Ranthalion/ButtonRelayControl/firmware/ButtonRelayControl/ButtonRelayControl/src/driver_init.c

/**
 * \file
 *
 * \brief Driver initialization.
 *
 (c) 2018 Microchip Technology Inc. and its subsidiaries.

    Subject to your compliance with these terms,you may use this software and
    any derivatives exclusively with Microchip products.It is your responsibility
    to comply with third party license terms applicable to your use of third party
    software (including open source software) that may accompany Microchip software.

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
    IN NO EVENT WILL MICROCHIP BE LIABLE FOR ANY INDIRECT, SPECIAL, PUNITIVE,
    INCIDENTAL OR CONSEQUENTIAL LOSS, DAMAGE, COST OR EXPENSE OF ANY KIND
    WHATSOEVER RELATED TO THE SOFTWARE, HOWEVER CAUSED, EVEN IF MICROCHIP HAS
    BEEN ADVISED OF THE POSSIBILITY OR THE DAMAGES ARE FORESEEABLE. TO THE
    FULLEST EXTENT ALLOWED BY LAW, MICROCHIP'S TOTAL LIABILITY ON ALL CLAIMS IN
    ANY WAY RELATED TO THIS SOFTWARE WILL NOT EXCEED THE AMOUNT OF FEES, IF ANY,
    THAT YOU HAVE PAID DIRECTLY TO MICROCHIP FOR THIS SOFTWARE.
 *
 */

/*
 * Code generated by START.
 *
 * This file will be overwritten when reconfiguring your START project.
 * Please copy examples or other code you want to keep to a separate file
 * to avoid losing it when reconfiguring.
 */

#include "driver_init.h"
#include <system.h>

void EXTERNAL_IRQ_0_initialization(void)
{

	// Set pin direction to input
	SW1_set_dir(PORT_DIR_IN);

	SW1_set_pull_mode(
	    // <y> Pull configuration
	    // <id> pad_pull_config
	    // <PORT_PULL_OFF"> Off
	    // <PORT_PULL_UP"> Pull-up
	    PORT_PULL_UP);

	// Set pin direction to input
	SENS2_set_dir(PORT_DIR_IN);

	SENS2_set_pull_mode(
	    // <y> Pull configuration
	    // <id> pad_pull_config
	    // <PORT_PULL_OFF"> Off
	    // <PORT_PULL_UP"> Pull-up
	    PORT_PULL_OFF);

	// Set pin direction to input
	SENS1_set_dir(PORT_DIR_IN);

	SENS1_set_pull_mode(
	    // <y> Pull configuration
	    // <id> pad_pull_config
	    // <PORT_PULL_OFF"> Off
	    // <PORT_PULL_UP"> Pull-up
	    PORT_PULL_OFF);

	// Set pin direction to input
	SW2_set_dir(PORT_DIR_IN);

	SW2_set_pull_mode(
	    // <y> Pull configuration
	    // <id> pad_pull_config
	    // <PORT_PULL_OFF"> Off
	    // <PORT_PULL_UP"> Pull-up
	    PORT_PULL_UP);

	EXTERNAL_IRQ_0_init();
}

void LED_SW2_initialization(void)
{

	// Set pin direction to output
	PD6_set_dir(PORT_DIR_OUT);

	PD6_set_level(
	    // <y> Initial level
	    // <id> pad_initial_level
	    // <false"> Low
	    // <true"> High
	    true);

	LED_SW2_init();
}

void LED_SW1_initialization(void)
{

	// Set pin direction to output
	PB1_set_dir(PORT_DIR_OUT);

	PB1_set_level(
	    // <y> Initial level
	    // <id> pad_initial_level
	    // <false"> Low
	    // <true"> High
	    true);

	LED_SW1_init();
}

void TIMER_0_initialization(void)
{

	TIMER_0_timeout_init();
}

/**
 * \brief System initialization
 */
void system_init()
{
	mcu_init();

	/* PORT setting on PB6 */

	// Set pin direction to output
	RELAY1_set_dir(PORT_DIR_OUT);

	RELAY1_set_level(
	    // <y> Initial level
	    // <id> pad_initial_level
	    // <false"> Low
	    // <true"> High
	    false);

	/* PORT setting on PD0 */

	// Set pin direction to output
	LED_set_dir(PORT_DIR_OUT);

	LED_set_level(
	    // <y> Initial level
	    // <id> pad_initial_level
	    // <false"> Low
	    // <true"> High
	    true);

	/* PORT setting on PE1 */

	// Set pin direction to output
	RELAY2_set_dir(PORT_DIR_OUT);

	RELAY2_set_level(
	    // <y> Initial level
	    // <id> pad_initial_level
	    // <false"> Low
	    // <true"> High
	    false);

	sysctrl_init();

	EXTERNAL_IRQ_0_initialization();

	LED_SW2_initialization();

	LED_SW1_initialization();

	TIMER_0_initialization();
}
