Ranthalion/ButtonRelayControl/firmware/ButtonRelayControl/ButtonRelayControl/src/timeout.c

/**
 * \file
 *
 * \brief Timeout driver.
 *
 (c) 2018 Microchip Technology Inc. and its subsidiaries.

    Subject to your compliance with these terms,you may use this software and
    any derivatives exclusively with Microchip products.It is your responsibility
    to comply with third party license terms applicable to your use of third party
    software (including open source software) that may accompany Microchip software.

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
    IN NO EVENT WILL MICROCHIP BE LIABLE FOR ANY INDIRECT, SPECIAL, PUNITIVE,
    INCIDENTAL OR CONSEQUENTIAL LOSS, DAMAGE, COST OR EXPENSE OF ANY KIND
    WHATSOEVER RELATED TO THE SOFTWARE, HOWEVER CAUSED, EVEN IF MICROCHIP HAS
    BEEN ADVISED OF THE POSSIBILITY OR THE DAMAGES ARE FORESEEABLE. TO THE
    FULLEST EXTENT ALLOWED BY LAW, MICROCHIP'S TOTAL LIABILITY ON ALL CLAIMS IN
    ANY WAY RELATED TO THIS SOFTWARE WILL NOT EXCEED THE AMOUNT OF FEES, IF ANY,
    THAT YOU HAVE PAID DIRECTLY TO MICROCHIP FOR THIS SOFTWARE.
 *
 */

/**
 \defgroup doc_driver_timer_timeout Timeout Driver
 \ingroup doc_driver_timer

 \section doc_driver_timer_timeout_rev Revision History
 - v0.0.0.1 Initial Commit

@{
*/
#include <stdio.h>
#include "timeout.h"
#include "atomic.h"

absolutetime_t TIMER_0_dummy_handler(void *payload)
{
	return 0;
};

void           TIMER_0_start_timer_at_head(void);
void           TIMER_0_enqueue_callback(timer_struct_t *timer);
void           TIMER_0_set_timer_duration(absolutetime_t duration);
absolutetime_t TIMER_0_make_absolute(absolutetime_t timeout);
absolutetime_t TIMER_0_rebase_list(void);

timer_struct_t *TIMER_0_list_head          = NULL;
timer_struct_t *TIMER_0_execute_queue_head = NULL;

timer_struct_t          TIMER_0_dummy                         = {TIMER_0_dummy_handler};
volatile absolutetime_t TIMER_0_absolute_time_of_last_timeout = 0;
volatile absolutetime_t TIMER_0_last_timer_load               = 0;
volatile bool           TIMER_0_is_running                    = false;

void TIMER_0_timeout_init(void)
{

	/* Enable TC3 */
	PRR1 &= ~(1 << PRTIM3);

	// TCCR3A = (0 << COM3A1) | (0 << COM3A0) /* Normal port operation, OCA disconnected */
	//		 | (0 << COM3B1) | (0 << COM3B0) /* Normal port operation, OCB disconnected */
	//		 | (0 << WGM31) | (0 << WGM30); /* Timeout */

	TCCR3B = (0 << WGM33) | (0 << WGM32)                /* Timeout */
	         | 0 << ICNC3                               /* Input Capture Noise Canceler: disabled */
	         | 0 << ICES3                               /* Input Capture Edge Select: disabled */
	         | (1 << CS32) | (0 << CS31) | (1 << CS30); /* IO clock divided by 1024 */

	TIMSK3 = 0 << OCIE3B   /* Output Compare B Match Interrupt Enable: disabled */
	         | 0 << OCIE3A /* Output Compare A Match Interrupt Enable: disabled */
	         | 0 << ICIE3  /* Input Capture Interrupt Enable: disabled */
	         | 1 << TOIE3; /* Overflow Interrupt Enable: enabled */
}

// Disable all the timers without deleting them from any list. Timers can be
//    restarted by calling startTimerAtHead
void TIMER_0_stop_timeouts(void)
{
	TIMSK3 &= ~(1 << TOIE3);

	TIMER_0_absolute_time_of_last_timeout = 0;
	TIMER_0_is_running                    = 0;
}

inline void TIMER_0_set_timer_duration(absolutetime_t duration)
{
	TIMER_0_last_timer_load = 65535 - duration;
	TCNT3                   = TIMER_0_last_timer_load;
}

// Convert the time provided from a "relative to now" time to a absolute time which
//    means ticks since the last timeout occurred or the timer module was started
inline absolutetime_t TIMER_0_make_absolute(absolutetime_t timeout)
{
	timeout += TIMER_0_absolute_time_of_last_timeout;
	if (TIMER_0_is_running) {
		timeout += TCNT3 - TIMER_0_last_timer_load;
	}
	return timeout;
}

// Adjust the time base so that we can never wrap, saving us a lot of complications
inline absolutetime_t TIMER_0_rebase_list(void)
{
	timer_struct_t *base_point = TIMER_0_list_head;
	absolutetime_t  base       = TIMER_0_list_head->absolute_time;

	while (base_point != NULL) {
		base_point->absolute_time -= base;
		base_point = base_point->next;
	}

	TIMER_0_absolute_time_of_last_timeout -= base;
	return base;
}

inline void TIMER_0_print_list(void)
{
	timer_struct_t *base_point = TIMER_0_list_head;
	while (base_point != NULL) {
		printf("%ld -> ", (uint32_t)base_point->absolute_time);
		base_point = base_point->next;
	}
	printf("NULL\n");
}

// Returns true if the insert was at the head, false if not
bool TIMER_0_sorted_insert(timer_struct_t *timer)
{
	absolutetime_t  timer_absolute_time = timer->absolute_time;
	uint8_t         at_head             = 1;
	timer_struct_t *insert_point        = TIMER_0_list_head;
	timer_struct_t *prev_point          = NULL;
	timer->next                         = NULL;

	if (timer_absolute_time < TIMER_0_absolute_time_of_last_timeout) {
		timer_absolute_time += 65535 - TIMER_0_rebase_list() + 1;
		timer->absolute_time = timer_absolute_time;
	}

	while (insert_point != NULL) {
		if (insert_point->absolute_time > timer_absolute_time) {
			break; // found the spot
		}
		prev_point   = insert_point;
		insert_point = insert_point->next;
		at_head      = 0;
	}

	if (at_head == 1) // the front of the list.
	{
		TIMER_0_set_timer_duration(65535);
		TIFR3 |= (1 << TOV3);

		timer->next       = (TIMER_0_list_head == &TIMER_0_dummy) ? TIMER_0_dummy.next : TIMER_0_list_head;
		TIMER_0_list_head = timer;
		return true;
	} else // middle of the list
	{
		timer->next = prev_point->next;
	}
	prev_point->next = timer;
	return false;
}

void TIMER_0_start_timer_at_head(void)
{
	TIMSK3 &= ~(1 << TOIE3);

	if (TIMER_0_list_head == NULL) // no timeouts left
	{
		TIMER_0_stop_timeouts();
		return;
	}

	absolutetime_t period = ((TIMER_0_list_head != NULL) ? (TIMER_0_list_head->absolute_time) : 0)
	                        - TIMER_0_absolute_time_of_last_timeout;

	// Timer is too far, insert dummy and schedule timer after the dummy
	if (period > 65535) {
		TIMER_0_dummy.absolute_time = TIMER_0_absolute_time_of_last_timeout + 65535;
		TIMER_0_dummy.next          = TIMER_0_list_head;
		TIMER_0_list_head           = &TIMER_0_dummy;
		period                      = 65535;
	}

	TIMER_0_set_timer_duration(period);

	TIMSK3 |= (1 << TOIE3);

	TIMER_0_is_running = 1;
}

// Cancel and remove all active timers
void TIMER_0_timeout_flush_all(void)
{
	TIMER_0_stop_timeouts();

	while (TIMER_0_list_head != NULL)
		TIMER_0_timeout_delete(TIMER_0_list_head);

	while (TIMER_0_execute_queue_head != NULL)
		TIMER_0_timeout_delete(TIMER_0_execute_queue_head);
}

// Deletes a timer from a list and returns true if the timer was found and
//     removed from the list specified
bool TIMER_0_timeout_delete_helper(timer_struct_t *volatile *list, timer_struct_t *timer)
{
	bool ret_val = false;
	if (*list == NULL)
		return ret_val;

	// Guard in case we get interrupted, we cannot safely compare/search and get interrupted
	TIMSK3 &= ~(1 << TOIE3);

	// Special case, the head is the one we are deleting
	if (timer == *list) {
		*list   = (*list)->next; // Delete the head
		ret_val = true;
		TIMER_0_start_timer_at_head(); // Start the new timer at the head
	} else {                           // More than one timer in the list, search the list.
		timer_struct_t *find_timer = *list;
		timer_struct_t *prev_timer = NULL;
		while (find_timer != NULL) {
			if (find_timer == timer) {
				prev_timer->next = find_timer->next;
				ret_val          = true;
				break;
			}
			prev_timer = find_timer;
			find_timer = find_timer->next;
		}
		TIMSK3 |= (1 << TOIE3);
	}

	return ret_val;
}

// This will cancel/remove a running timer. If the timer is already expired it will
//     also remove it from the callback queue
void TIMER_0_timeout_delete(timer_struct_t *timer)
{
	if (!TIMER_0_timeout_delete_helper(&TIMER_0_list_head, timer)) {
		TIMER_0_timeout_delete_helper(&TIMER_0_execute_queue_head, timer);
	}

	timer->next = NULL;
}

// Moves the timer from the active list to the list of timers which are expired and
//    needs their callbacks called in call_next_callback
inline void TIMER_0_enqueue_callback(timer_struct_t *timer)
{
	timer_struct_t *tmp;
	timer->next = NULL;

	// Special case for empty list
	if (TIMER_0_execute_queue_head == NULL) {
		TIMER_0_execute_queue_head = timer;
		return;
	}

	// Find the end of the list and insert the next expired timer at the back of the queue
	tmp = TIMER_0_execute_queue_head;
	while (tmp->next != NULL)
		tmp = tmp->next;

	tmp->next = timer;
}

// This function checks the list of expired timers and calls the first one in the
//    list if the list is not empty. It also reschedules the timer if the callback
//    returned a value greater than 0
// It is recommended this is called from the main superloop (while(1)) in your code
//    but by design this can also be called from the timer ISR. If you wish callbacks
//    to happen from the ISR context you can call this as the last action in timeout_isr
//    instead.
void TIMER_0_timeout_call_next_callback(void)
{

	if (TIMER_0_execute_queue_head == NULL)
		return;

	// Critical section needed if TIMER_0_timeout_call_next_callback()
	// was called from polling loop, and not called from ISR.
	ENTER_CRITICAL(T);
	timer_struct_t *callback_timer = TIMER_0_execute_queue_head;

	// Done, remove from list
	TIMER_0_execute_queue_head = TIMER_0_execute_queue_head->next;
	// Mark the timer as not in use
	callback_timer->next = NULL;
	EXIT_CRITICAL(T); // End critical section

	absolutetime_t reschedule = callback_timer->callback_ptr(callback_timer->payload);

	// Do we have to reschedule it? If yes then add delta to absolute for reschedule
	if (reschedule) {
		TIMER_0_timeout_create(callback_timer, reschedule);
	}
}

// This function starts the timer provided with an expiry equal to "timeout".
// If the timer was already active/running it will be replaced by this and the
//    old (active) timer will be removed/cancelled first
void TIMER_0_timeout_create(timer_struct_t *timer, absolutetime_t timeout)
{
	TIMSK3 &= ~(1 << TOIE3);

	// If this timer is already active, replace it
	TIMER_0_timeout_delete(timer);

	timer->absolute_time = TIMER_0_make_absolute(timeout);

	// We only have to start the timer at head if the insert was at the head
	if (TIMER_0_sorted_insert(timer)) {
		TIMER_0_start_timer_at_head();
	} else {
		if (TIMER_0_is_running)
			TIMSK3 |= (1 << TOIE3);
	}
}

// NOTE: assumes the callback completes before the next timer tick
ISR(TIMER3_OVF_vect)
{
	timer_struct_t *next                  = TIMER_0_list_head->next;
	TIMER_0_absolute_time_of_last_timeout = TIMER_0_list_head->absolute_time;
	TIMER_0_last_timer_load               = 0;

	if (TIMER_0_list_head != &TIMER_0_dummy)
		TIMER_0_enqueue_callback(TIMER_0_list_head);

	// Remove expired timer for the list now (it is always the one at the head)
	TIMER_0_list_head = next;

	TIMER_0_start_timer_at_head();
}

// These methods are for calculating the elapsed time in stopwatch mode.
// TIMER_0_timeout_start_timer will start a
// timer with (maximum range)/2. You cannot time more than
// this and the timer will stop after this time elapses
void TIMER_0_timeout_start_timer(timer_struct_t *timer)
{
	absolutetime_t i = -1;
	TIMER_0_timeout_create(timer, i >> 1);
}

// This funciton stops the "stopwatch" and returns the elapsed time.
absolutetime_t TIMER_0_timeout_stop_timer(timer_struct_t *timer)
{
	absolutetime_t now = TIMER_0_make_absolute(0); // Do this as fast as possible for accuracy
	absolutetime_t i   = -1;
	i >>= 1;

	TIMER_0_timeout_delete(timer);

	absolutetime_t diff = timer->absolute_time - now;

	// This calculates the (max range)/2 minus (remaining time) which = elapsed time
	return (i - diff);
}
