Ranthalion/ButtonRelayControl/firmware/ButtonRelayControl/ButtonRelayControl/include/atmel_start_pins.h

/*
 * Code generated from Atmel Start.
 *
 * This file will be overwritten when reconfiguring your Atmel Start project.
 * Please copy examples or other code you want to keep to a separate file
 * to avoid losing it when reconfiguring.
 */
#ifndef ATMEL_START_PINS_H_INCLUDED
#define ATMEL_START_PINS_H_INCLUDED

#include <port.h>

/**
 * \brief Set PB1 pull mode
 *
 * Configure pin to pull up, down or disable pull mode, supported pull
 * modes are defined by device used
 *
 * \param[in] pull_mode Pin pull mode
 */
static inline void PB1_set_pull_mode(const enum port_pull_mode pull_mode)
{
	PORTB_set_pin_pull_mode(1, pull_mode);
}

/**
 * \brief Set PB1 data direction
 *
 * Select if the pin data direction is input, output or disabled.
 * If disabled state is not possible, this function throws an assert.
 *
 * \param[in] direction PORT_DIR_IN  = Data direction in
 *                      PORT_DIR_OUT = Data direction out
 *                      PORT_DIR_OFF = Disables the pin
 *                      (low power state)
 */
static inline void PB1_set_dir(const enum port_dir dir)
{
	PORTB_set_pin_dir(1, dir);
}

/**
 * \brief Set PB1 level
 *
 * Sets output level on a pin
 *
 * \param[in] level true  = Pin level set to "high" state
 *                  false = Pin level set to "low" state
 */
static inline void PB1_set_level(const bool level)
{
	PORTB_set_pin_level(1, level);
}

/**
 * \brief Toggle output level on PB1
 *
 * Toggle the pin level
 */
static inline void PB1_toggle_level()
{
	PORTB_toggle_pin_level(1);
}

/**
 * \brief Get level on PB1
 *
 * Reads the level on a pin
 */
static inline bool PB1_get_level()
{
	return PORTB_get_pin_level(1);
}

/**
 * \brief Set SW1 pull mode
 *
 * Configure pin to pull up, down or disable pull mode, supported pull
 * modes are defined by device used
 *
 * \param[in] pull_mode Pin pull mode
 */
static inline void SW1_set_pull_mode(const enum port_pull_mode pull_mode)
{
	PORTB_set_pin_pull_mode(2, pull_mode);
}

/**
 * \brief Set SW1 data direction
 *
 * Select if the pin data direction is input, output or disabled.
 * If disabled state is not possible, this function throws an assert.
 *
 * \param[in] direction PORT_DIR_IN  = Data direction in
 *                      PORT_DIR_OUT = Data direction out
 *                      PORT_DIR_OFF = Disables the pin
 *                      (low power state)
 */
static inline void SW1_set_dir(const enum port_dir dir)
{
	PORTB_set_pin_dir(2, dir);
}

/**
 * \brief Set SW1 level
 *
 * Sets output level on a pin
 *
 * \param[in] level true  = Pin level set to "high" state
 *                  false = Pin level set to "low" state
 */
static inline void SW1_set_level(const bool level)
{
	PORTB_set_pin_level(2, level);
}

/**
 * \brief Toggle output level on SW1
 *
 * Toggle the pin level
 */
static inline void SW1_toggle_level()
{
	PORTB_toggle_pin_level(2);
}

/**
 * \brief Get level on SW1
 *
 * Reads the level on a pin
 */
static inline bool SW1_get_level()
{
	return PORTB_get_pin_level(2);
}

/**
 * \brief Set RELAY1 pull mode
 *
 * Configure pin to pull up, down or disable pull mode, supported pull
 * modes are defined by device used
 *
 * \param[in] pull_mode Pin pull mode
 */
static inline void RELAY1_set_pull_mode(const enum port_pull_mode pull_mode)
{
	PORTB_set_pin_pull_mode(6, pull_mode);
}

/**
 * \brief Set RELAY1 data direction
 *
 * Select if the pin data direction is input, output or disabled.
 * If disabled state is not possible, this function throws an assert.
 *
 * \param[in] direction PORT_DIR_IN  = Data direction in
 *                      PORT_DIR_OUT = Data direction out
 *                      PORT_DIR_OFF = Disables the pin
 *                      (low power state)
 */
static inline void RELAY1_set_dir(const enum port_dir dir)
{
	PORTB_set_pin_dir(6, dir);
}

/**
 * \brief Set RELAY1 level
 *
 * Sets output level on a pin
 *
 * \param[in] level true  = Pin level set to "high" state
 *                  false = Pin level set to "low" state
 */
static inline void RELAY1_set_level(const bool level)
{
	PORTB_set_pin_level(6, level);
}

/**
 * \brief Toggle output level on RELAY1
 *
 * Toggle the pin level
 */
static inline void RELAY1_toggle_level()
{
	PORTB_toggle_pin_level(6);
}

/**
 * \brief Get level on RELAY1
 *
 * Reads the level on a pin
 */
static inline bool RELAY1_get_level()
{
	return PORTB_get_pin_level(6);
}

/**
 * \brief Set LED pull mode
 *
 * Configure pin to pull up, down or disable pull mode, supported pull
 * modes are defined by device used
 *
 * \param[in] pull_mode Pin pull mode
 */
static inline void LED_set_pull_mode(const enum port_pull_mode pull_mode)
{
	PORTD_set_pin_pull_mode(0, pull_mode);
}

/**
 * \brief Set LED data direction
 *
 * Select if the pin data direction is input, output or disabled.
 * If disabled state is not possible, this function throws an assert.
 *
 * \param[in] direction PORT_DIR_IN  = Data direction in
 *                      PORT_DIR_OUT = Data direction out
 *                      PORT_DIR_OFF = Disables the pin
 *                      (low power state)
 */
static inline void LED_set_dir(const enum port_dir dir)
{
	PORTD_set_pin_dir(0, dir);
}

/**
 * \brief Set LED level
 *
 * Sets output level on a pin
 *
 * \param[in] level true  = Pin level set to "high" state
 *                  false = Pin level set to "low" state
 */
static inline void LED_set_level(const bool level)
{
	PORTD_set_pin_level(0, level);
}

/**
 * \brief Toggle output level on LED
 *
 * Toggle the pin level
 */
static inline void LED_toggle_level()
{
	PORTD_toggle_pin_level(0);
}

/**
 * \brief Get level on LED
 *
 * Reads the level on a pin
 */
static inline bool LED_get_level()
{
	return PORTD_get_pin_level(0);
}

/**
 * \brief Set SENS2 pull mode
 *
 * Configure pin to pull up, down or disable pull mode, supported pull
 * modes are defined by device used
 *
 * \param[in] pull_mode Pin pull mode
 */
static inline void SENS2_set_pull_mode(const enum port_pull_mode pull_mode)
{
	PORTD_set_pin_pull_mode(2, pull_mode);
}

/**
 * \brief Set SENS2 data direction
 *
 * Select if the pin data direction is input, output or disabled.
 * If disabled state is not possible, this function throws an assert.
 *
 * \param[in] direction PORT_DIR_IN  = Data direction in
 *                      PORT_DIR_OUT = Data direction out
 *                      PORT_DIR_OFF = Disables the pin
 *                      (low power state)
 */
static inline void SENS2_set_dir(const enum port_dir dir)
{
	PORTD_set_pin_dir(2, dir);
}

/**
 * \brief Set SENS2 level
 *
 * Sets output level on a pin
 *
 * \param[in] level true  = Pin level set to "high" state
 *                  false = Pin level set to "low" state
 */
static inline void SENS2_set_level(const bool level)
{
	PORTD_set_pin_level(2, level);
}

/**
 * \brief Toggle output level on SENS2
 *
 * Toggle the pin level
 */
static inline void SENS2_toggle_level()
{
	PORTD_toggle_pin_level(2);
}

/**
 * \brief Get level on SENS2
 *
 * Reads the level on a pin
 */
static inline bool SENS2_get_level()
{
	return PORTD_get_pin_level(2);
}

/**
 * \brief Set SENS1 pull mode
 *
 * Configure pin to pull up, down or disable pull mode, supported pull
 * modes are defined by device used
 *
 * \param[in] pull_mode Pin pull mode
 */
static inline void SENS1_set_pull_mode(const enum port_pull_mode pull_mode)
{
	PORTD_set_pin_pull_mode(3, pull_mode);
}

/**
 * \brief Set SENS1 data direction
 *
 * Select if the pin data direction is input, output or disabled.
 * If disabled state is not possible, this function throws an assert.
 *
 * \param[in] direction PORT_DIR_IN  = Data direction in
 *                      PORT_DIR_OUT = Data direction out
 *                      PORT_DIR_OFF = Disables the pin
 *                      (low power state)
 */
static inline void SENS1_set_dir(const enum port_dir dir)
{
	PORTD_set_pin_dir(3, dir);
}

/**
 * \brief Set SENS1 level
 *
 * Sets output level on a pin
 *
 * \param[in] level true  = Pin level set to "high" state
 *                  false = Pin level set to "low" state
 */
static inline void SENS1_set_level(const bool level)
{
	PORTD_set_pin_level(3, level);
}

/**
 * \brief Toggle output level on SENS1
 *
 * Toggle the pin level
 */
static inline void SENS1_toggle_level()
{
	PORTD_toggle_pin_level(3);
}

/**
 * \brief Get level on SENS1
 *
 * Reads the level on a pin
 */
static inline bool SENS1_get_level()
{
	return PORTD_get_pin_level(3);
}

/**
 * \brief Set PD6 pull mode
 *
 * Configure pin to pull up, down or disable pull mode, supported pull
 * modes are defined by device used
 *
 * \param[in] pull_mode Pin pull mode
 */
static inline void PD6_set_pull_mode(const enum port_pull_mode pull_mode)
{
	PORTD_set_pin_pull_mode(6, pull_mode);
}

/**
 * \brief Set PD6 data direction
 *
 * Select if the pin data direction is input, output or disabled.
 * If disabled state is not possible, this function throws an assert.
 *
 * \param[in] direction PORT_DIR_IN  = Data direction in
 *                      PORT_DIR_OUT = Data direction out
 *                      PORT_DIR_OFF = Disables the pin
 *                      (low power state)
 */
static inline void PD6_set_dir(const enum port_dir dir)
{
	PORTD_set_pin_dir(6, dir);
}

/**
 * \brief Set PD6 level
 *
 * Sets output level on a pin
 *
 * \param[in] level true  = Pin level set to "high" state
 *                  false = Pin level set to "low" state
 */
static inline void PD6_set_level(const bool level)
{
	PORTD_set_pin_level(6, level);
}

/**
 * \brief Toggle output level on PD6
 *
 * Toggle the pin level
 */
static inline void PD6_toggle_level()
{
	PORTD_toggle_pin_level(6);
}

/**
 * \brief Get level on PD6
 *
 * Reads the level on a pin
 */
static inline bool PD6_get_level()
{
	return PORTD_get_pin_level(6);
}

/**
 * \brief Set SW2 pull mode
 *
 * Configure pin to pull up, down or disable pull mode, supported pull
 * modes are defined by device used
 *
 * \param[in] pull_mode Pin pull mode
 */
static inline void SW2_set_pull_mode(const enum port_pull_mode pull_mode)
{
	PORTD_set_pin_pull_mode(7, pull_mode);
}

/**
 * \brief Set SW2 data direction
 *
 * Select if the pin data direction is input, output or disabled.
 * If disabled state is not possible, this function throws an assert.
 *
 * \param[in] direction PORT_DIR_IN  = Data direction in
 *                      PORT_DIR_OUT = Data direction out
 *                      PORT_DIR_OFF = Disables the pin
 *                      (low power state)
 */
static inline void SW2_set_dir(const enum port_dir dir)
{
	PORTD_set_pin_dir(7, dir);
}

/**
 * \brief Set SW2 level
 *
 * Sets output level on a pin
 *
 * \param[in] level true  = Pin level set to "high" state
 *                  false = Pin level set to "low" state
 */
static inline void SW2_set_level(const bool level)
{
	PORTD_set_pin_level(7, level);
}

/**
 * \brief Toggle output level on SW2
 *
 * Toggle the pin level
 */
static inline void SW2_toggle_level()
{
	PORTD_toggle_pin_level(7);
}

/**
 * \brief Get level on SW2
 *
 * Reads the level on a pin
 */
static inline bool SW2_get_level()
{
	return PORTD_get_pin_level(7);
}

/**
 * \brief Set RELAY2 pull mode
 *
 * Configure pin to pull up, down or disable pull mode, supported pull
 * modes are defined by device used
 *
 * \param[in] pull_mode Pin pull mode
 */
static inline void RELAY2_set_pull_mode(const enum port_pull_mode pull_mode)
{
	PORTE_set_pin_pull_mode(1, pull_mode);
}

/**
 * \brief Set RELAY2 data direction
 *
 * Select if the pin data direction is input, output or disabled.
 * If disabled state is not possible, this function throws an assert.
 *
 * \param[in] direction PORT_DIR_IN  = Data direction in
 *                      PORT_DIR_OUT = Data direction out
 *                      PORT_DIR_OFF = Disables the pin
 *                      (low power state)
 */
static inline void RELAY2_set_dir(const enum port_dir dir)
{
	PORTE_set_pin_dir(1, dir);
}

/**
 * \brief Set RELAY2 level
 *
 * Sets output level on a pin
 *
 * \param[in] level true  = Pin level set to "high" state
 *                  false = Pin level set to "low" state
 */
static inline void RELAY2_set_level(const bool level)
{
	PORTE_set_pin_level(1, level);
}

/**
 * \brief Toggle output level on RELAY2
 *
 * Toggle the pin level
 */
static inline void RELAY2_toggle_level()
{
	PORTE_toggle_pin_level(1);
}

/**
 * \brief Get level on RELAY2
 *
 * Reads the level on a pin
 */
static inline bool RELAY2_get_level()
{
	return PORTE_get_pin_level(1);
}

#endif /* ATMEL_START_PINS_H_INCLUDED */
